Taro-Hayashi/Shotgun-CherryPie/AcrylicCase/img/IMG_8778.jpeg

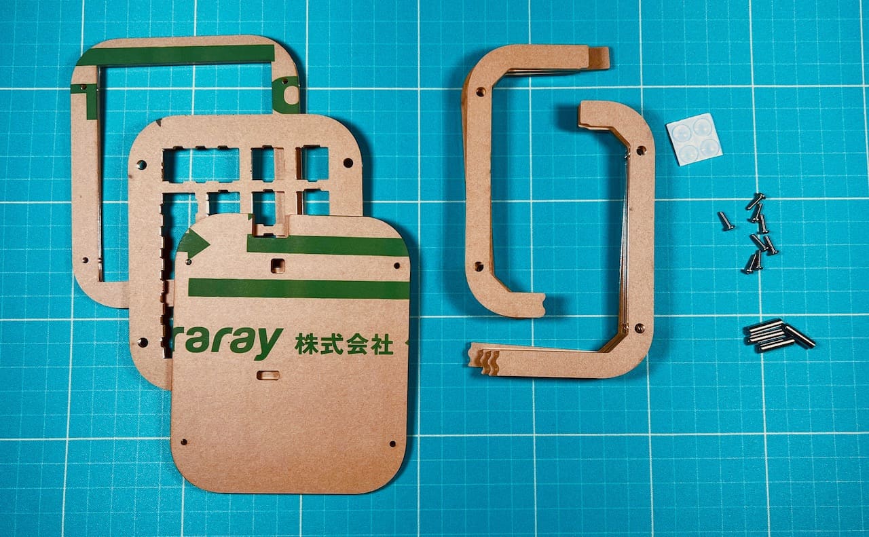
AcrylicCase/img/IMG_8778.jpeg
