Taro-Hayashi/Shotgun-CherryPie/AcrylicCase/img/shotgun_cpc.jpeg

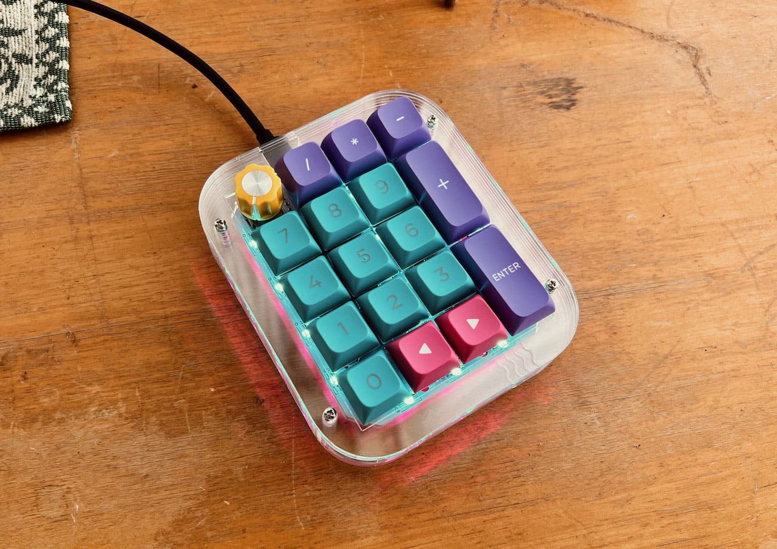
AcrylicCase/img/shotgun_cpc.jpeg
