Taro-Hayashi/Shotgun-CherryPie/img/default.png

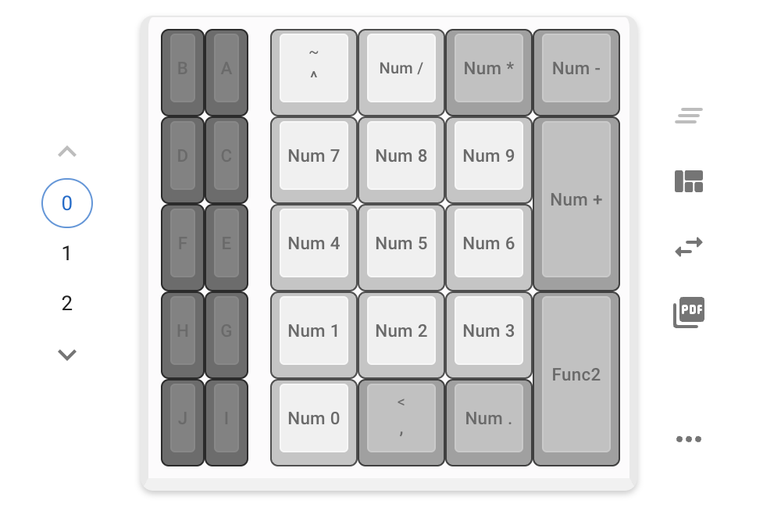
img/default.png
