Taro-Hayashi/Shotgun-CherryPie/img/func.png

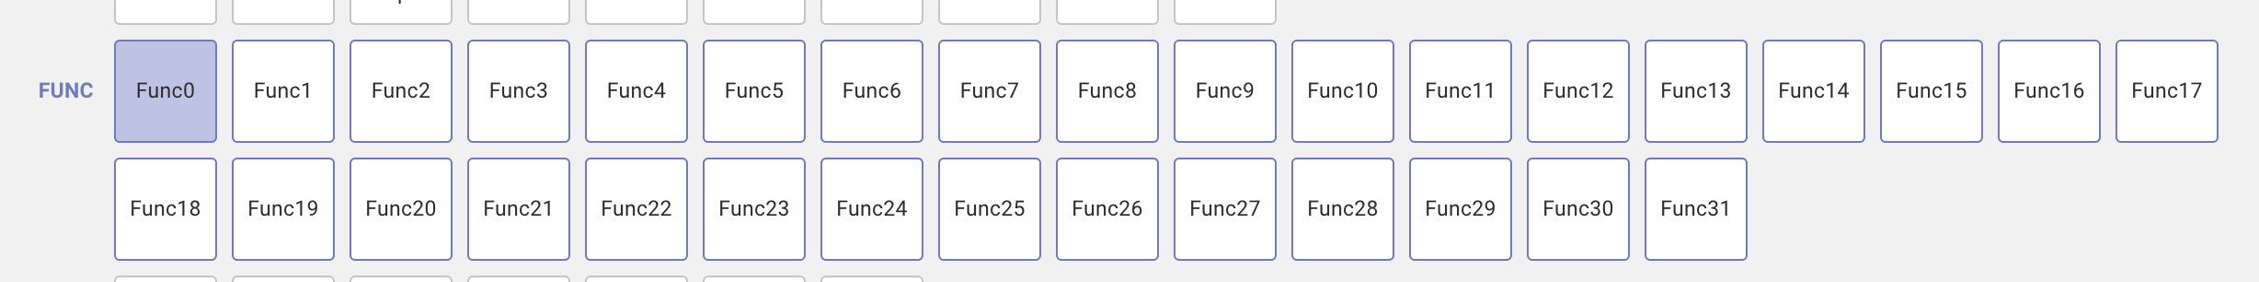
img/func.png
