Taro-Hayashi/Shotgun-CherryPie/img/IMG_3529.jpeg

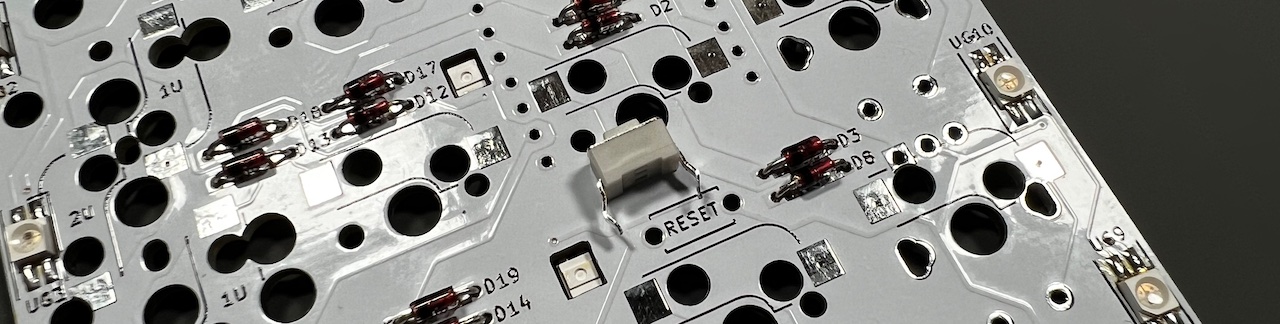
img/IMG_3529.jpeg
