Taro-Hayashi/Shotgun-CherryPie/img/IMG_4382.jpg

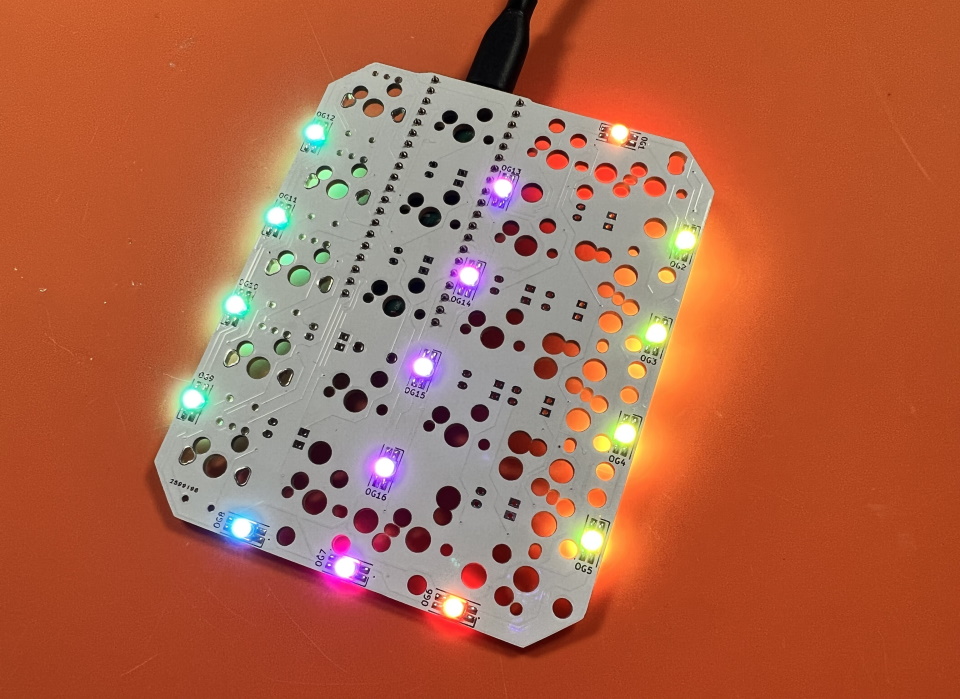
img/IMG_4382.jpg
