Taro-Hayashi/Shotgun-CherryPie/img/IMG_4389.jpg

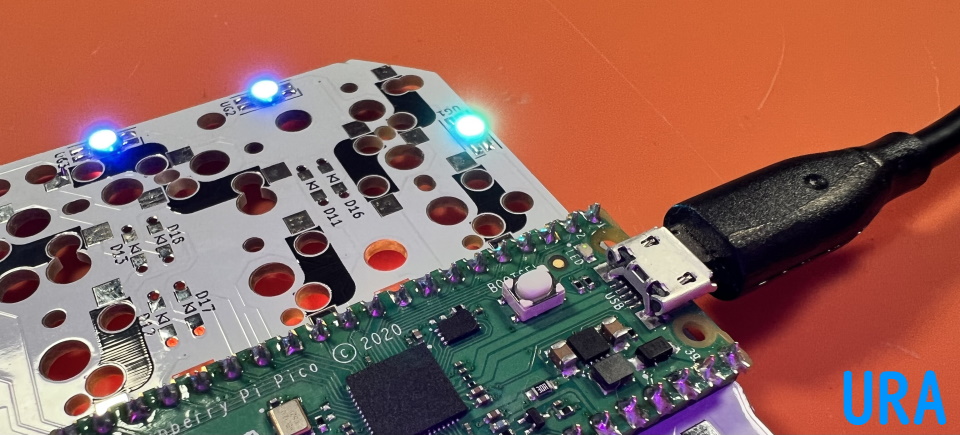
img/IMG_4389.jpg
