Taro-Hayashi/Shotgun-CherryPie/img/IMG_4447.jpg

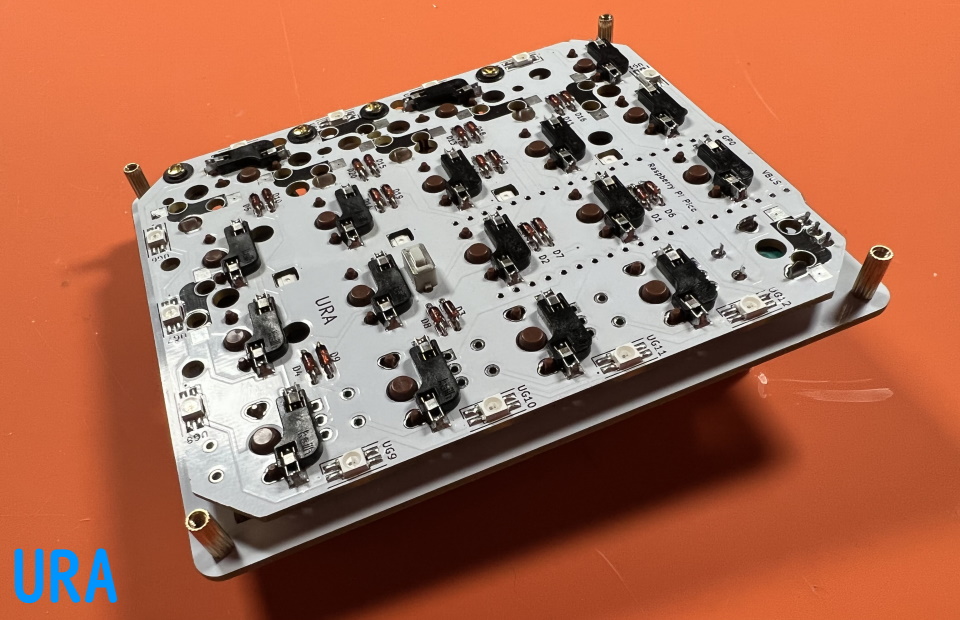
img/IMG_4447.jpg
