Taro-Hayashi/Shotgun-CherryPie/img/IMG_4448.jpg

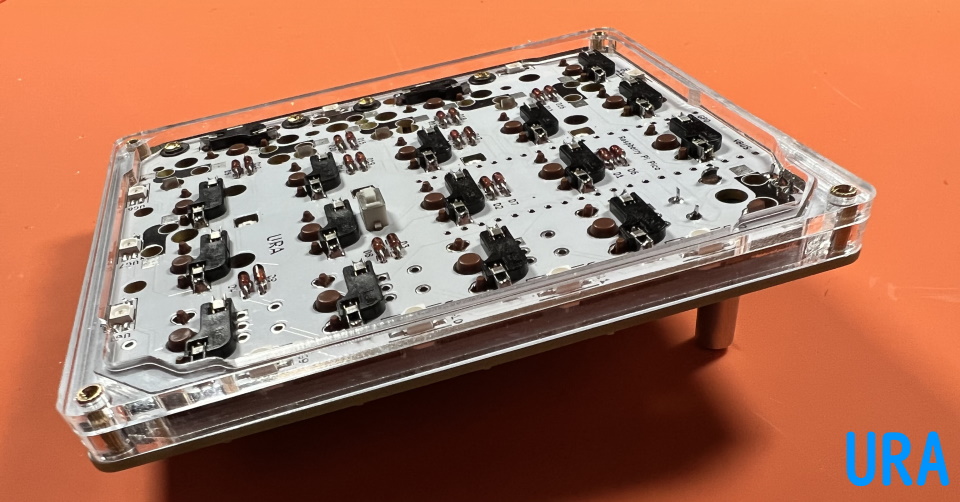
img/IMG_4448.jpg
