Taro-Hayashi/Shotgun-CherryPie/img/IMG_4937.jpg

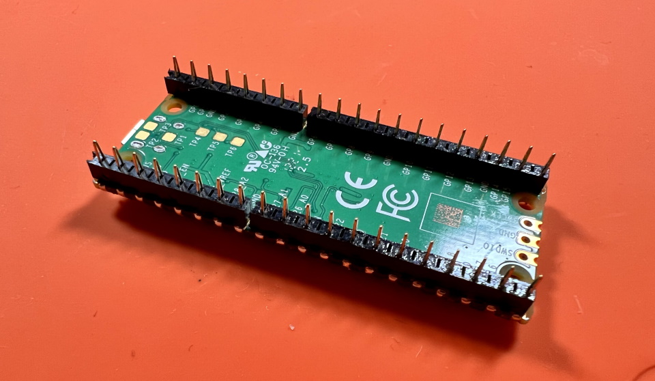
img/IMG_4937.jpg
