Taro-Hayashi/Shotgun-CherryPie/img/IMG_5639.jpg

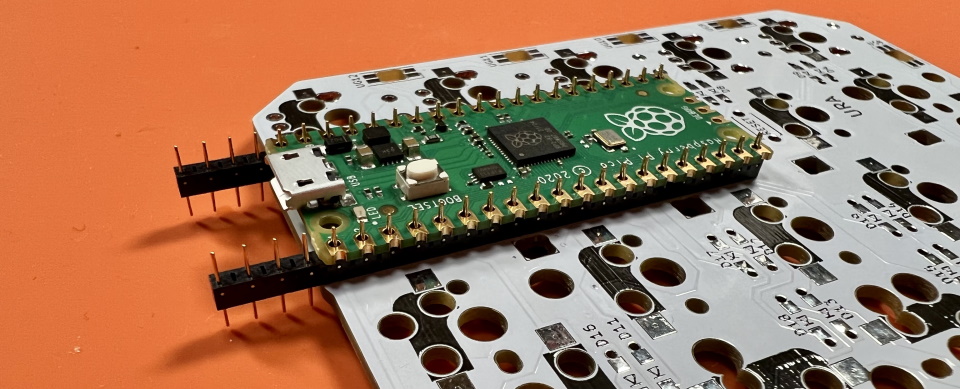
img/IMG_5639.jpg
