Taro-Hayashi/Shotgun-CherryPie/img/IMG_6043.JPEG

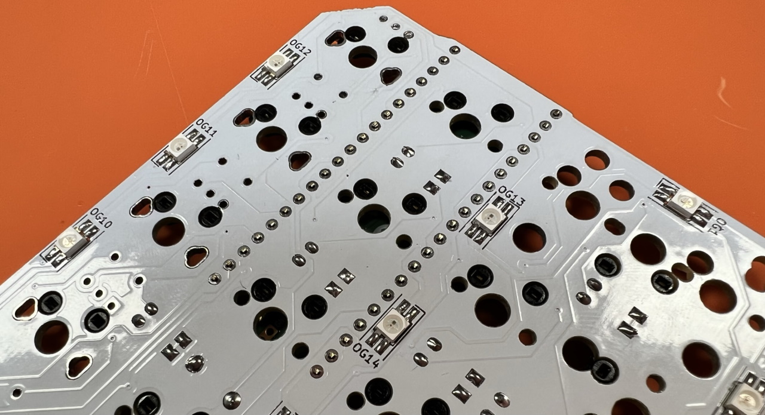
img/IMG_6043.JPEG
