Taro-Hayashi/Shotgun-CherryPie/img/led.jpg

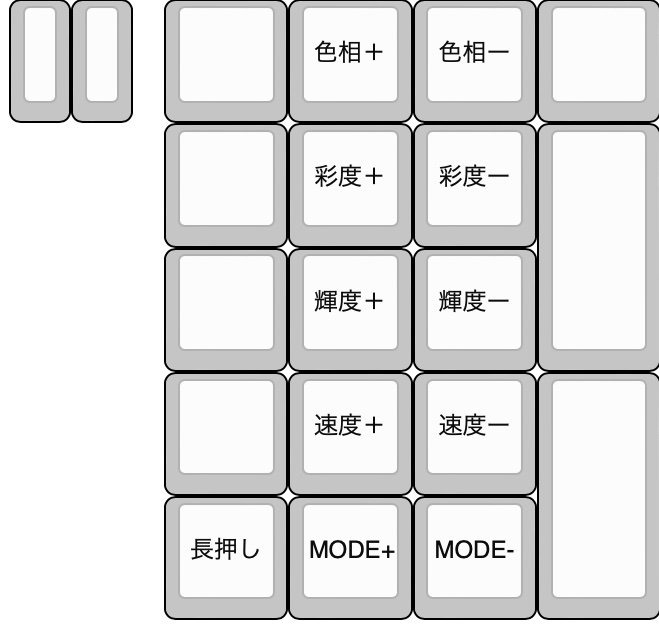
img/led.jpg
